Mposiblee/Zireael/photos/6.jpg

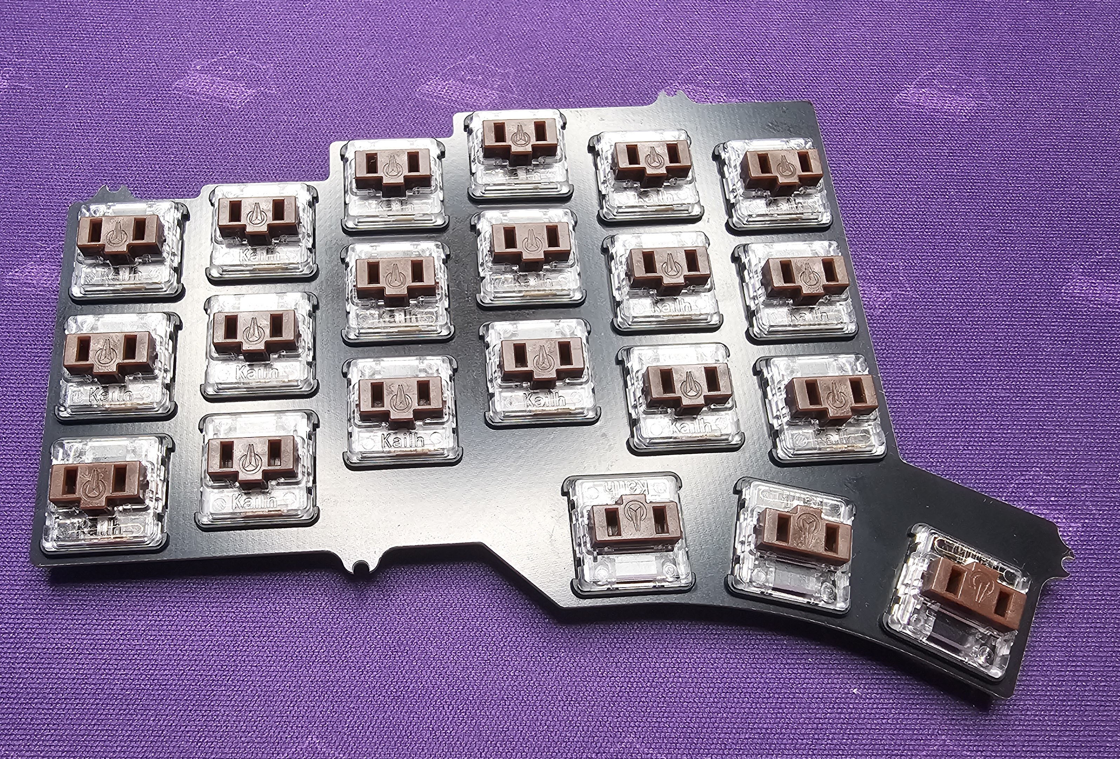
photos/6.jpg
