Mposiblee/Zireael/photos/7.jpg

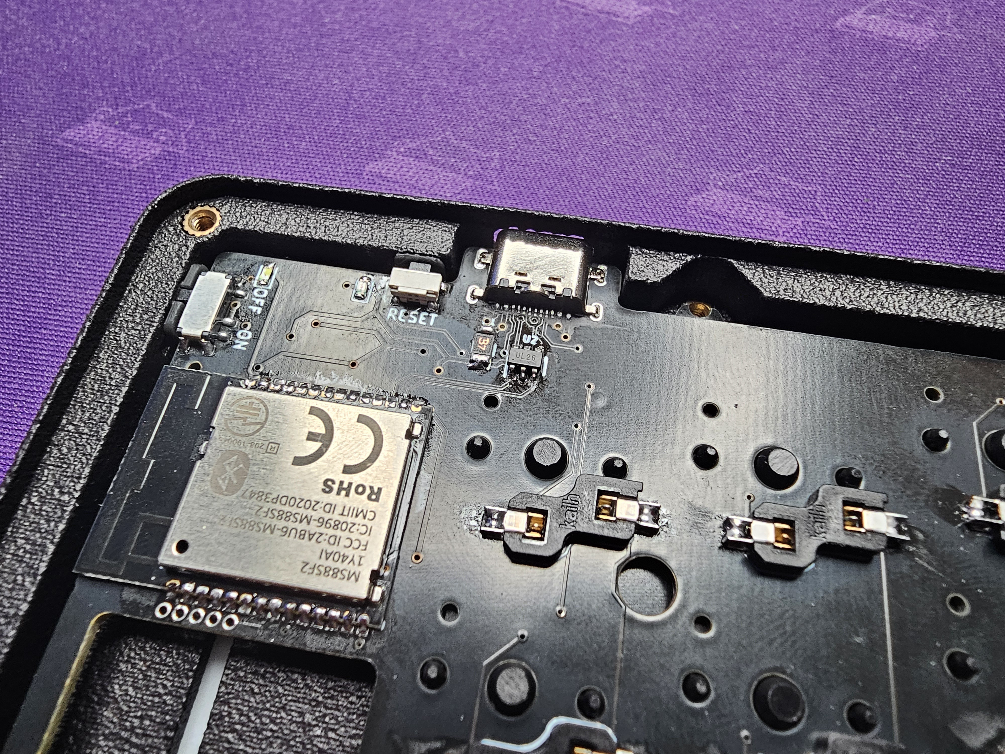
photos/7.jpg
